Goochy12/BA-Falcon-Custom-Climate-Control/resources/wiring colour codes.png

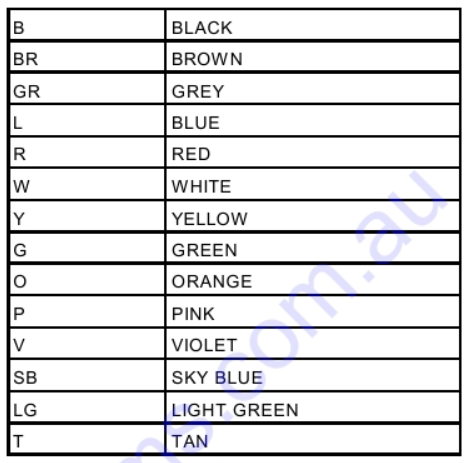
resources/wiring colour codes.png
